LuizPauloDamaceno/tractianchallenge/real_implementations_data/graphs_with_data/esp8266_file.png

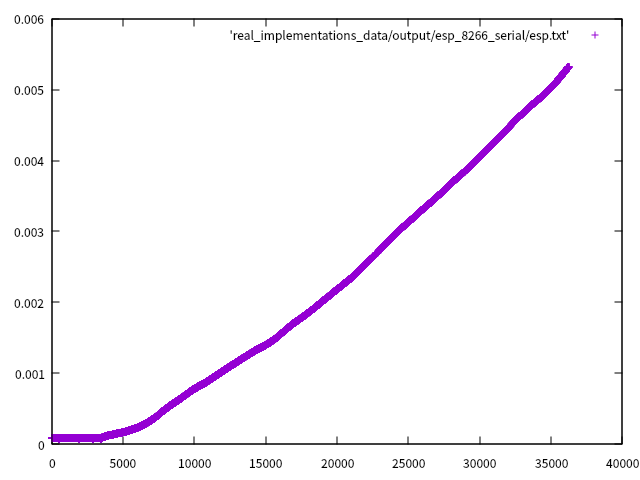
real_implementations_data/graphs_with_data/esp8266_file.png
